TechRandom/BlinkBoy/Code/Blink_Boy/text.h

#ifndef TEXT_H
#define TEXT_H

#include <FastLED.h>

#define TEXT_SPEED 100

extern CRGB textColor;

// Character definitions
// The first index of the array is the width of the character
const byte ZERO[] = {4, 0x3C, 0x42, 0x42, 0x3C};
const byte ONE[] = {3, 0x44, 0x7E, 0x40};
const byte TWO[] = {4, 0x64, 0x52, 0x4A, 0x44};
const byte THREE[] = {4, 0x44, 0x42, 0x4A, 0x34};
const byte FOUR[] = {4, 0x1E, 0x10, 0x10, 0x7E};
const byte FIVE[] = {4, 0x4E, 0x4A, 0x4A, 0x32};
const byte SIX[] = {4, 0x3C, 0x4A, 0x4A, 0x32};
const byte SEVEN[] = {4, 0x02, 0x72, 0x0A, 0x06};
const byte EIGHT[] = {4, 0x34, 0x4A, 0x4A, 0x34};
const byte NINE[] = {4, 0x4C, 0x52, 0x52, 0x3C};
const byte A[] = {5, 0x78, 0x14, 0x12, 0x14, 0x78};
const byte B[] = {4, 0x7E, 0x4A, 0x4A, 0x34};
const byte C[] = {4, 0x3C, 0x42, 0x42, 0x24};
const byte D[] = {4, 0x7E, 0x42, 0x42, 0x3C};
const byte E[] = {4, 0x7E, 0x4A, 0x4A, 0x42};
const byte F[] = {4, 0x7E, 0x0A, 0x0A, 0x02};
const byte G[] = {4, 0x3C, 0x42, 0x52, 0x34};
const byte H[] = {4, 0x7E, 0x08, 0x08, 0x7E};
const byte I[] = {3, 0x42, 0x7E, 0x42};
const byte J[] = {4, 0x20, 0x40, 0x42, 0x3E};
const byte K[] = {4, 0x7E, 0x08, 0x14, 0x62};
const byte L[] = {3, 0x7E, 0x40, 0x40};
const byte M[] = {5, 0x7E, 0x04, 0x08, 0x04, 0x7E};
const byte N[] = {4, 0x7E, 0x04, 0x18, 0x7E};
const byte O[] = {4, 0x3C, 0x42, 0x42, 0x3C};
const byte P[] = {4, 0x7E, 0x12, 0x12, 0x0C};
const byte Q[] = {4, 0x3C, 0x42, 0x62, 0xBC};
const byte R[] = {4, 0x7E, 0x12, 0x32, 0x4C};
const byte S[] = {4, 0x4C, 0x4A, 0x4A, 0x32};
const byte T[] = {3, 0x02, 0x7E, 0x02};
const byte U[] = {4, 0x3E, 0x40, 0x40, 0x3E};
const byte V[] = {4, 0x1E, 0x60, 0x60, 0x1E};
const byte W[] = {4, 0x7E, 0x30, 0x30, 0x7E};
const byte X[] = {4, 0x66, 0x18, 0x18, 0x66};
const byte Y[] = {5, 0x06, 0x08, 0x70, 0x08, 0x06};
const byte Z[] = {4, 0x62, 0x52, 0x4A, 0x46};
const byte SPACE[] = {3, 0x00, 0x00, 0x00};

// Function headers
void startScrollText(const char* text, int delayTime);
void updateScrollText();
int displayChar(char c, int offset);
int getCharWidth(char c);

#endif // TEXT_H
